cburlacu/remote_switch/pcb/input_power_sim.asc

D1: zener; 1N750
D2: schottky; RB480Y
R1: res; 10k
V1: voltage; PULSE(0 25 0 .05 .05 0 .1)
V2: voltage; 5; Rser=.1
Named nets: 0
.tran 1s
